c3h899/Battery_Charger/Variable V Feedback/Draft1.asc

C1: cap; 10nF
C2: cap; 10nF
C3: cap; 10nF
D1: zener; BZX84C6V2L
R1: res; 5k
R2: res; 20k
R3: res; 4k
R4: res; 4k
U1: opamp
V1: voltage; SINE(24 12 200k); AC 12
Named nets: 0
.tran 0 10m 0 10u uic
.lib opamp.sub
-102 dBv @ 200 kHz
-68 dBv @ 200 kHz
-34 dBv @ 200 kHz
;ac dec 10000 100 1000000
1/50 V/V
1/2500 V/V
1/128000 V/V
~1 ms Transient Time
