c3h899/Battery_Charger/LTspice/Temp_Sensor.asc

R1: res; 18k
R2: res; 18k
R3: res; 18k
R4: res; 27k
R5: res; 5.33k
R6: res; 25.3k
R7: res; 27k
R8: res; 27k
V1: voltage; 2
Named nets: 0, Cold, Hot, TLO, THI
.tran 0 100m 0 100u
